cracked-machine/DigitalCurrentSinkV3/HW/docs/3D/CurrentSinkModule2.png

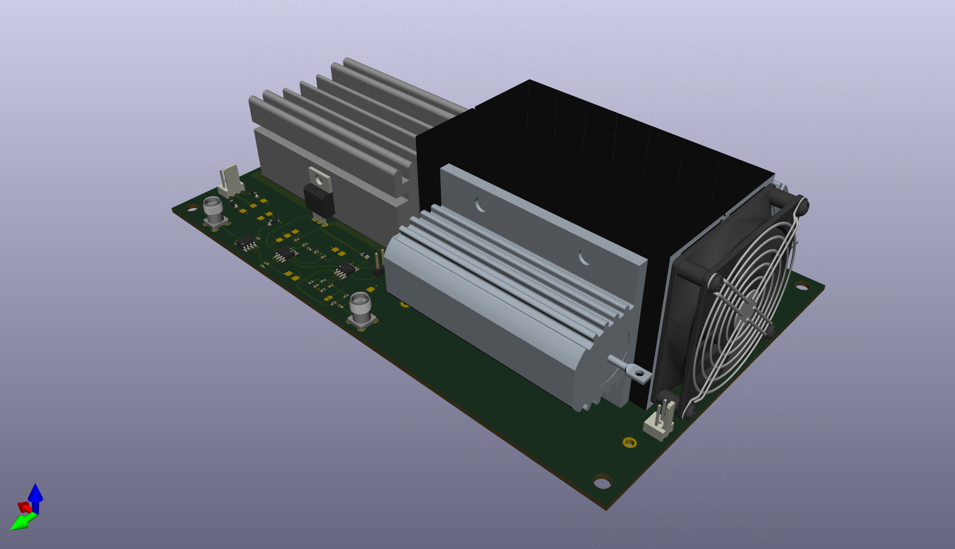
HW/docs/3D/CurrentSinkModule2.png
