cracked-machine/DigitalCurrentSinkV3/CAD/ControlModuleFrontPanel/doc/3D/ControlModuleFrontPanel_Notations.png

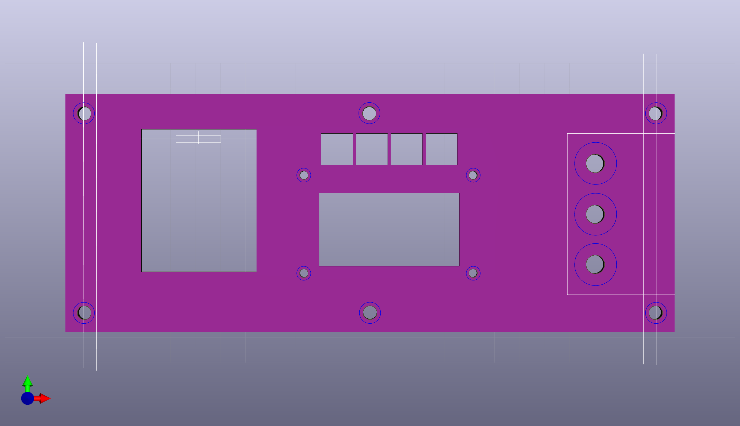
CAD/ControlModuleFrontPanel/doc/3D/ControlModuleFrontPanel_Notations.png
