cracked-machine/DigitalCurrentSinkV3/CAD/ControlModuleFrontPanel/doc/3D/ControlModuleFrontPanel_Realistic.png

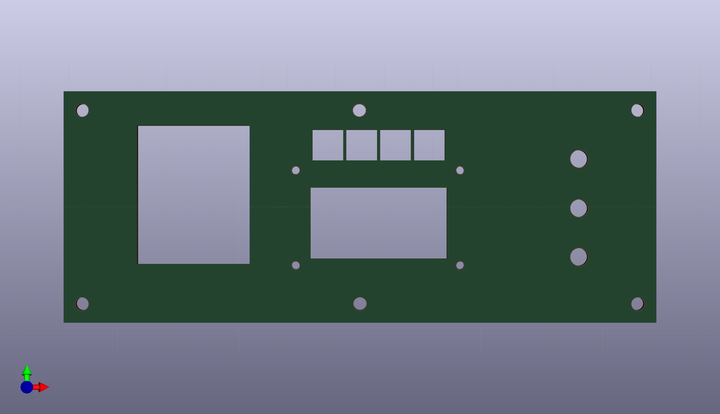
CAD/ControlModuleFrontPanel/doc/3D/ControlModuleFrontPanel_Realistic.png
