cracked-machine/DigitalCurrentSinkV3/HW/docs/3D/CurrentSinkModule.png

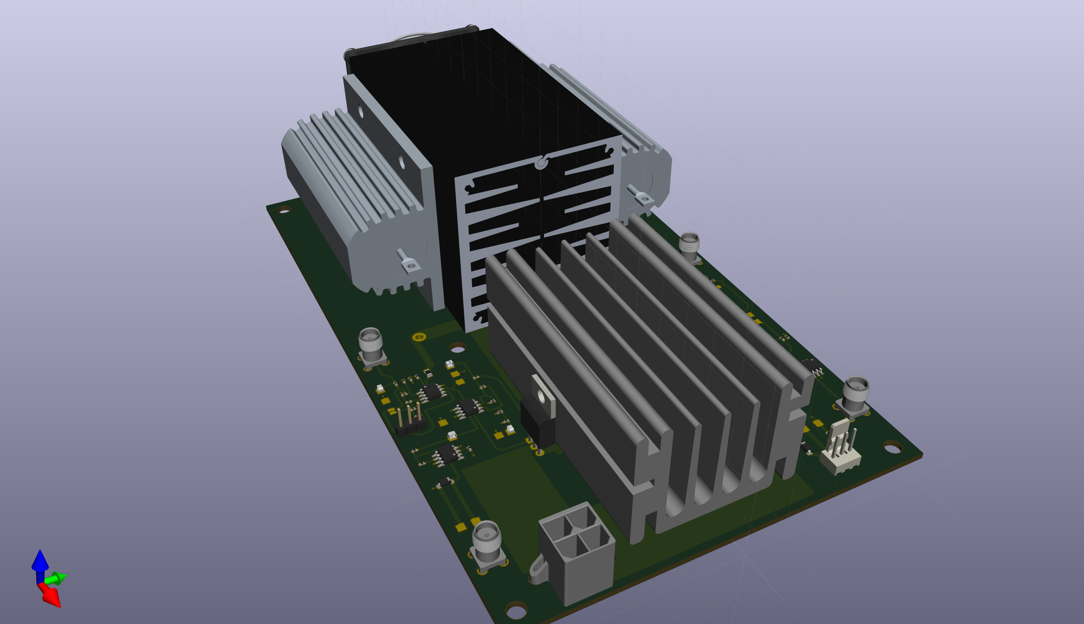
HW/docs/3D/CurrentSinkModule.png
