cracked-machine/DigitalCurrentSinkV3/HW/Simulation/ADA4522/NonInvertingx10Gain/NonInvertingx1.5Gain_GainAndNoise.png

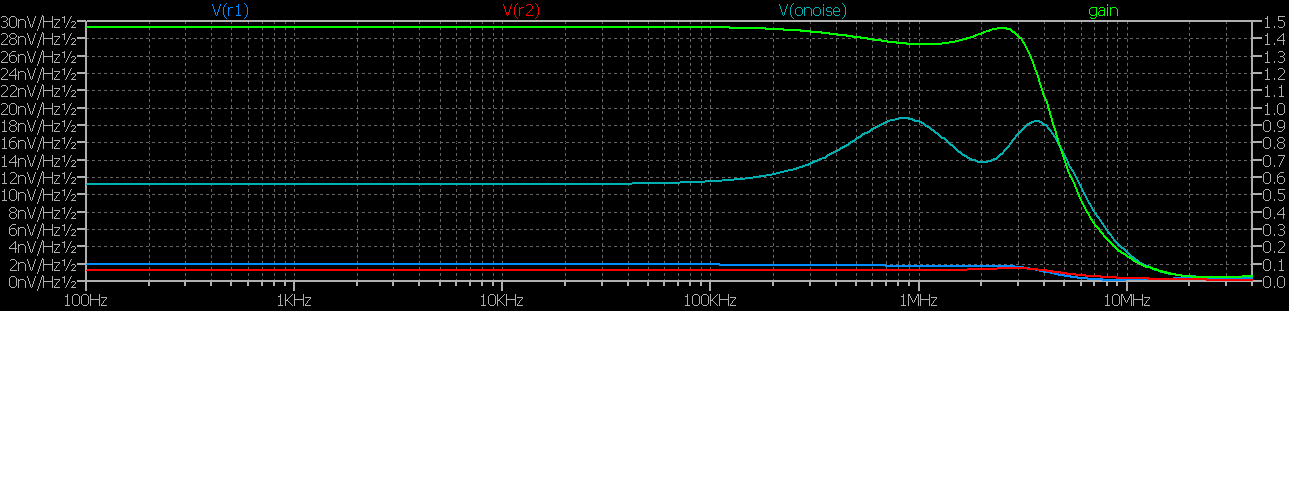
HW/Simulation/ADA4522/NonInvertingx10Gain/NonInvertingx1.5Gain_GainAndNoise.png
