cracked-machine/DigitalCurrentSinkV3/HW/Simulation/ADA4522/NonInvertingx10Gain/NonInvertingx10Gain.png

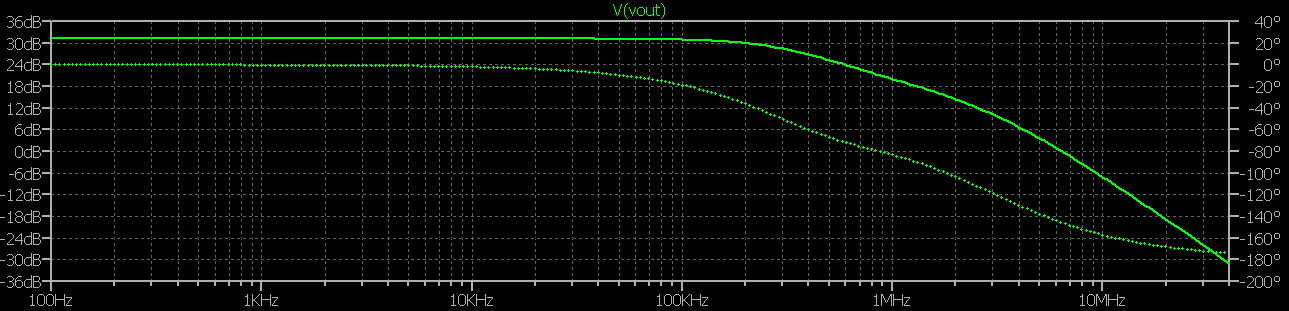
HW/Simulation/ADA4522/NonInvertingx10Gain/NonInvertingx10Gain.png
