cracked-machine/DigitalCurrentSinkV3/HW/Simulation/CurrentSenseResistor/LowSide.png

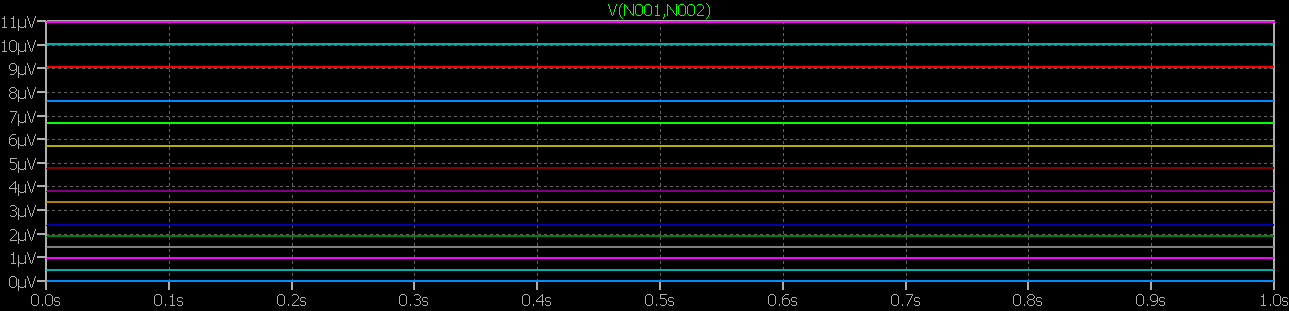
HW/Simulation/CurrentSenseResistor/LowSide.png
