cracked-machine/DigitalCurrentSinkV3/HW/Simulation/LTC2058/NonInvertingUnityGain/NonInvertingUnityGain_FreqVsGainAndNoise_Output.png

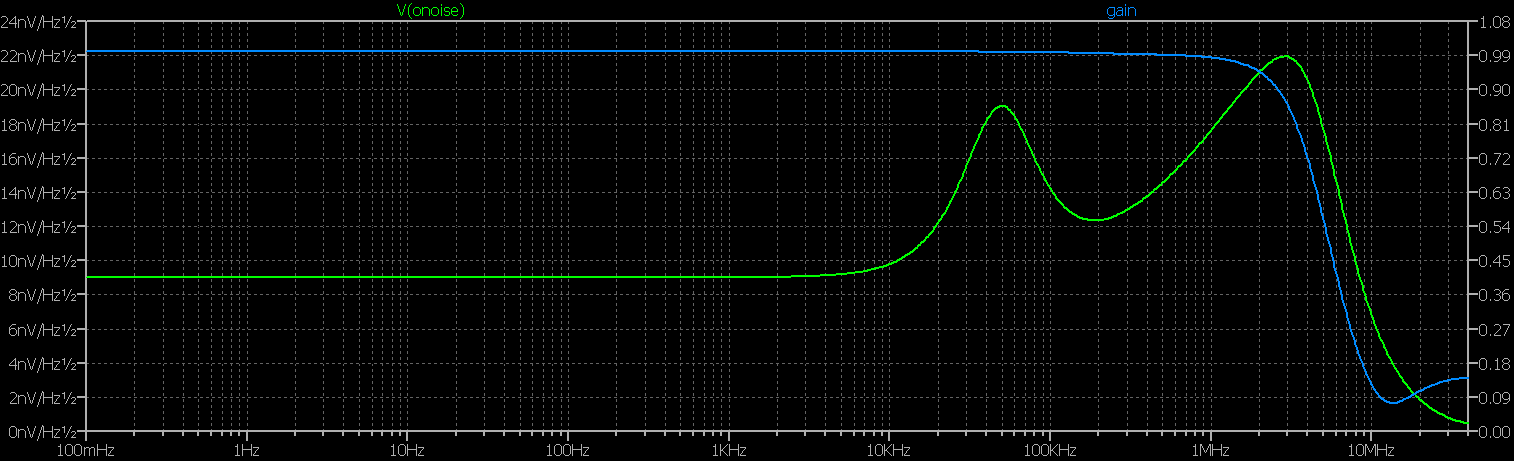
HW/Simulation/LTC2058/NonInvertingUnityGain/NonInvertingUnityGain_FreqVsGainAndNoise_Output.png
