cracked-machine/DigitalCurrentSinkV3/HW/Simulation/ADA4522/FirstOrderSK_LowPass/1stOrderLowsPass_NoiseRange1K_50K.png

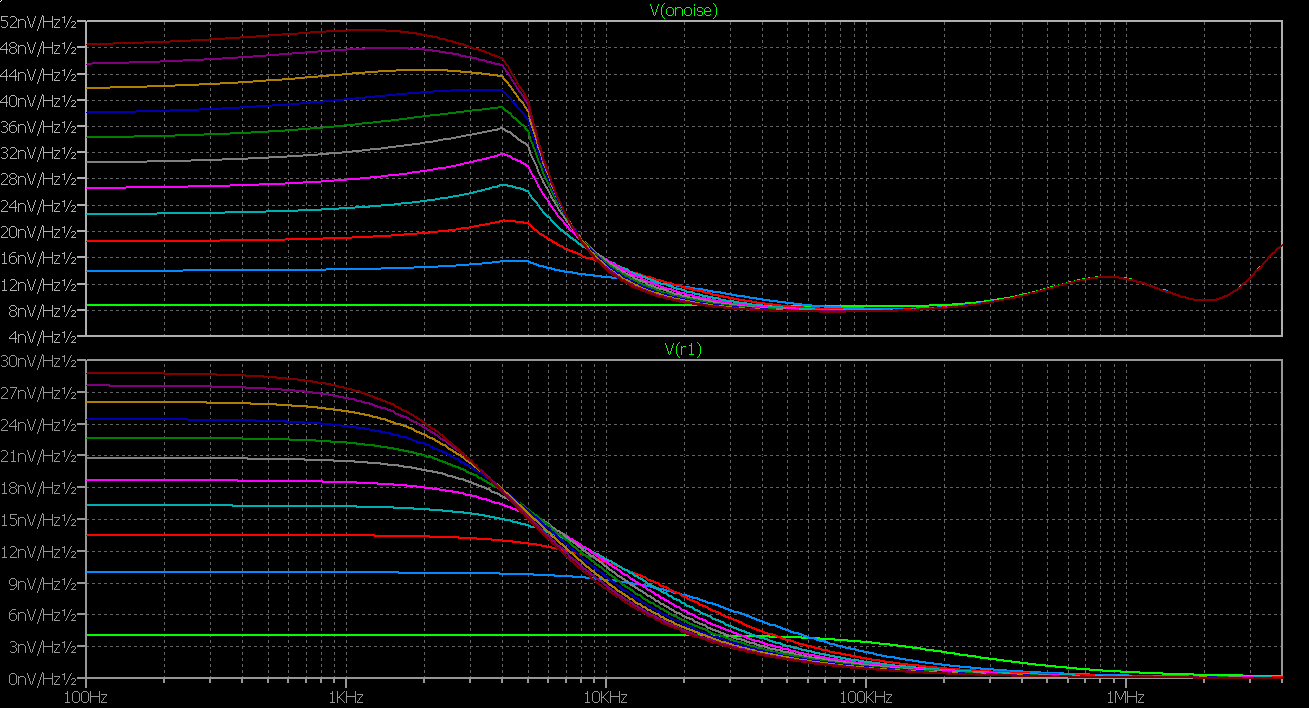
HW/Simulation/ADA4522/FirstOrderSK_LowPass/1stOrderLowsPass_NoiseRange1K_50K.png
