cracked-machine/DigitalCurrentSinkV3/HW/Simulation/ADA4522/FirstOrderSK_LowPass/1stOrderLowsPass_NoiseRange10R_100R.png

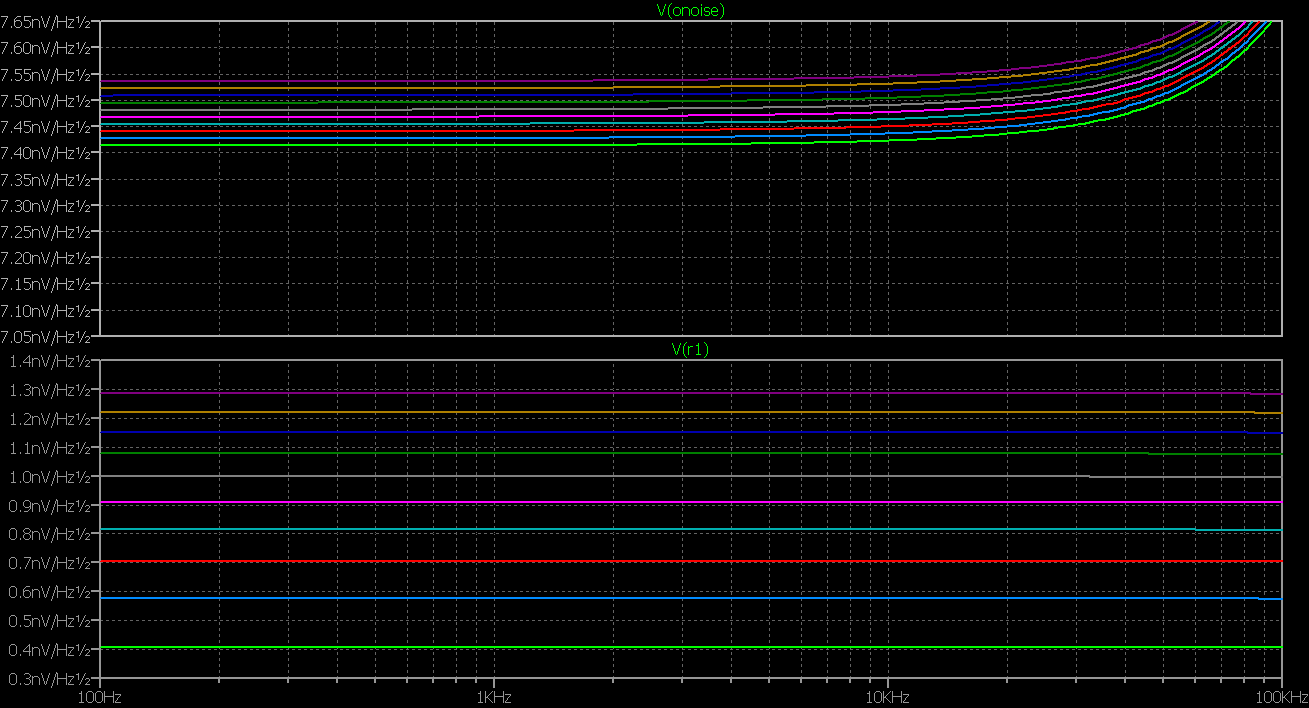
HW/Simulation/ADA4522/FirstOrderSK_LowPass/1stOrderLowsPass_NoiseRange10R_100R.png
