cracked-machine/DigitalCurrentSinkV3/HW/Simulation/ADA4522/SecondOrderSK_LowPass/2ndOrderSKLowPass_NoiseAndAtten_100R_10u.png

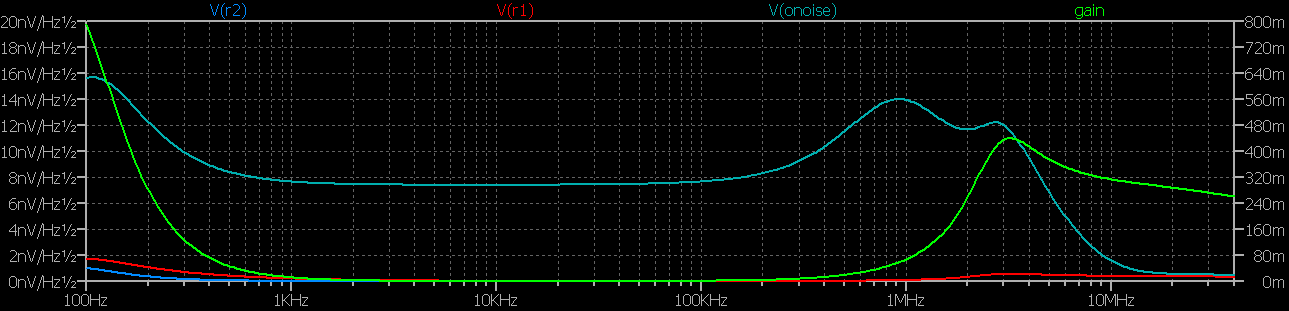
HW/Simulation/ADA4522/SecondOrderSK_LowPass/2ndOrderSKLowPass_NoiseAndAtten_100R_10u.png
