cracked-machine/DigitalCurrentSinkV3/HW/Simulation/LT1007/2ndOrderSKLowPass_/2ndOrderSKLowPass_NoiseAndAtten_1K_100n.png

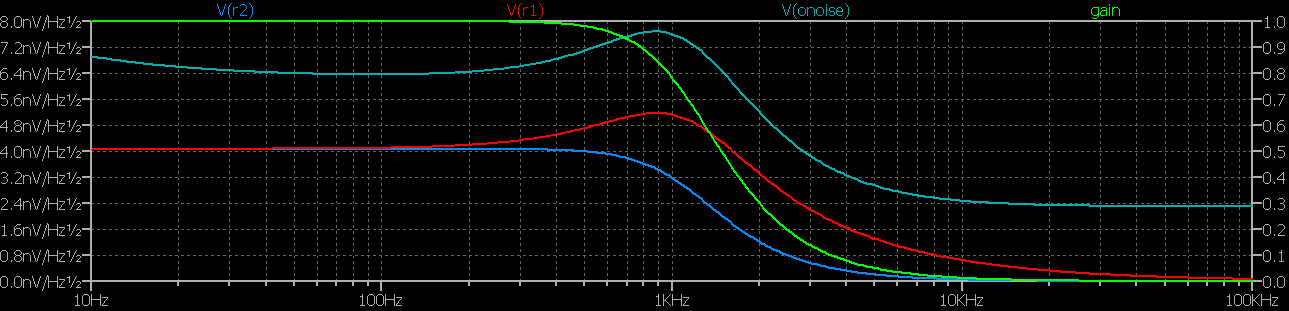
HW/Simulation/LT1007/2ndOrderSKLowPass_/2ndOrderSKLowPass_NoiseAndAtten_1K_100n.png
