cracked-machine/DigitalCurrentSinkV3/HW/Simulation/LTC2058/SecondOrderSK_LowPass/2ndOrderLowsPass_Noise100RWith0_10u.png

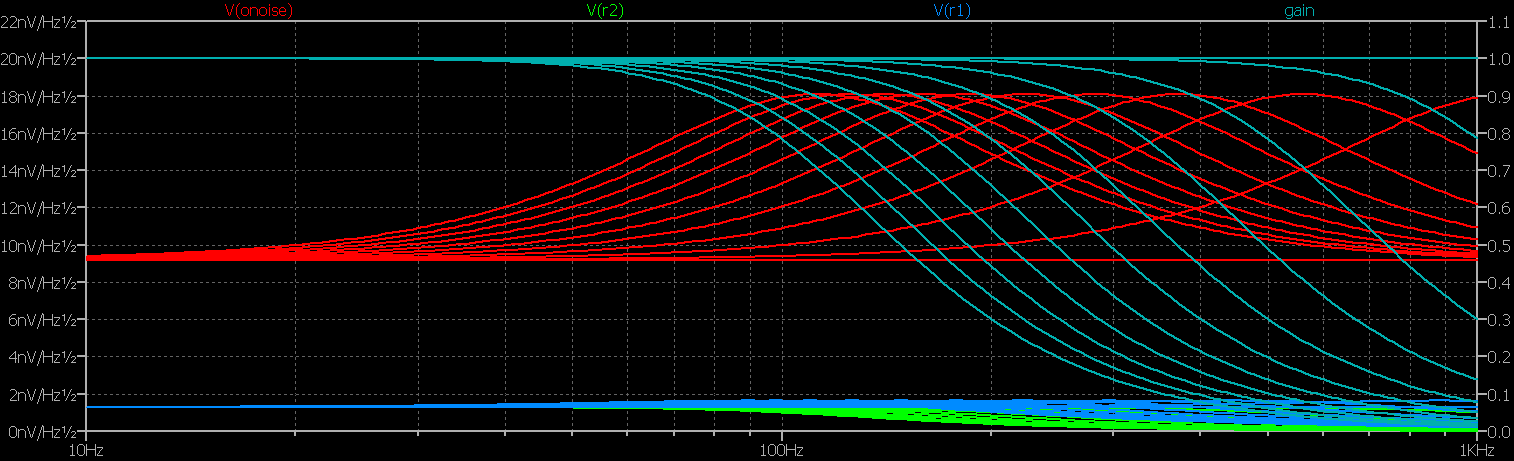
HW/Simulation/LTC2058/SecondOrderSK_LowPass/2ndOrderLowsPass_Noise100RWith0_10u.png
