cracked-machine/DigitalCurrentSinkV3/HW/Simulation/LTC2058/SecondOrderSK_LowPass/2ndOrderLowsPass_UnityGainAndNoise2x100RWith10u_AndResistorNoiseContributions.png

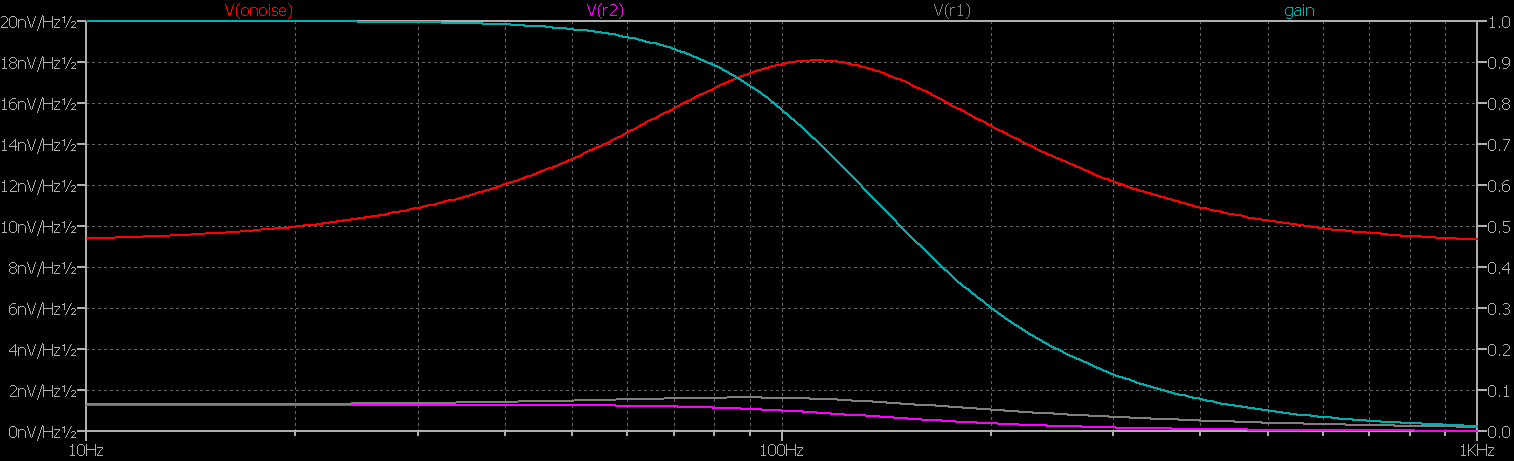
HW/Simulation/LTC2058/SecondOrderSK_LowPass/2ndOrderLowsPass_UnityGainAndNoise2x100RWith10u_AndResistorNoiseContributions.png
