cracked-machine/DigitalCurrentSinkV3/HW/Simulation/ADA4522/FirstOrderSK_LowPass/FirstOrderSK_LowPass.asc

C2: cap; {C1}
R1: res; 100R
U1: ADA4522-1
V1: voltage; 2.5
V2: voltage; 2.5
V3: voltage; ""; AC 1
Named nets: 0, V-, V+, Vout, Vin
.ac dec 100 100 40e6
.noise V(Vout) V3 dec 100 10 10K
.step param C1 0u 10u 1u
