cracked-machine/DigitalCurrentSinkV3/HW/Simulation/ADA4522/SecondOrderSK_LowPass/DRAFT13.ASC

C1: cap; 2n
C2: cap; 1n
R1: res; 5K
R2: res; 5K
U1: LT6020
V1: voltage; 5
V2: voltage; 5
V4: signal; SINE(0 1 100)
Named nets: 0, Vout, Vin, V+, V-
.tran 2
