cracked-machine/DigitalCurrentSinkV3/HW/Simulation/ADA4522/SecondOrderSK_LowPass/SecondOrderSK_LowPass.asc

C1: cap; 2µ
C2: cap; 1µ
R1: res; 10k
R2: res; 10k
U1: ADA4522-1
V1: voltage; 12
V2: voltage; 12
V3: voltage; ""; AC 1
Named nets: 0, V-, V+, Vout, Vin
.ac dec 100 100 40e6
.noise V(Vout) V3 dec 100 10 1K
