cracked-machine/DigitalCurrentSinkV3/HW/Simulation/LT1007/2ndOrderSKLowPass_/SecondOrderSK_LowPass.asc

C1: cap; 200n
C2: cap; 100n
R1: res; 1K
R2: res; 1K
U2: LT1007
V1: voltage; 12
V2: voltage; 12
V3: voltage; ""; AC 1
Named nets: 0, V-, V+, Vout, Vin
.ac dec 100 100 40e6
.noise V(Vout) V3 dec 100 10 100K
