cracked-machine/DigitalCurrentSinkV3/HW/Simulation/LTC2058/2ndOrderSK_LowPassWithSeperateGainStage/2ndOrderSK_LPFWithSeperateGainStage.asc

C1: cap; 20µ
C2: cap; 10µ
R1: res; 100R
R2: res; 100R
R3: res; 220R
R4: res; 470R
U1: LTC2058
U3: LTC2058
V1: voltage; 12
V2: voltage; 12
V3: voltage; ""; AC 1
Named nets: 0, V-, V+, Vout2, Vin, Vout1
.ac dec 100 100 40e6
;noise V(Vout1) V3 dec 100 10 1K
.STEP PARAM C1 0u 10u 1u
.noise V(Vout1) V3 dec 100 10 1K
