cracked-machine/DigitalCurrentSinkV3/HW/Simulation/ADA4522/SecondOrderSK_LowPass/DRAFT14.ASC

Q1: npn
V1: voltage; {Vin}
V2: voltage; 12V
Named nets: 0, V+
