cracked-machine/DigitalCurrentSinkV3/HW/Simulation/LTC2058/SecondOrderSK_LowPass/SecondOrderSK_LowPass.asc

C1: cap; {C1*2}
C2: cap; {C1}
R1: res; 100R
R2: res; 100R
R4: res; 220R
R5: res; 470R
U1: LTC2058
V1: voltage; 12
V2: voltage; 12
V3: voltage; ""; AC 1
Named nets: 0, V-, V+, Vout, Vin
.ac dec 100 100 40e6
.noise V(Vout) V3 dec 100 10 1K
.STEP PARAM C1 0u 10u 1u
