cracked-machine/DigitalCurrentSinkV3/HW/Simulation/MOSFET_CurrentSense_NoSignalInversion_AD8421.asc

M1: nmos
M2: pmos
R1: res; 0.33R
R2: res; 0.33R
R3: res; 10R
R4: res; 10R
U1: LTC2058
U2: LTC2058
U3: AD8421
U4: AD8421
V1: voltage; 15V
V2: voltage; 5V
V3: voltage; 5V
V4: voltage; {VPOSIN}
V5: voltage; 15V
V6: voltage; {VPOSIN}
Named nets: 0, V-, V+, VPOSOUT, VNEGOUT
.tran 1
.STEP PARAM VPOSIN 0.5 5 0.5
