cracked-machine/DigitalCurrentSinkV3/HW/Simulation/CurrentSenseResistor/CurrentSenseResistor_HighSide.ASC

C1: cap; 10n
C2: cap; 1n
C3: cap; 1n
C4: cap; 10n
C5: cap; 1n
C6: cap; 1n
M1: nmos
M2: pmos
R1: res; {Rsense}
R2: res; 5R
R3: res; 33R
R4: res; 33R
R5: res; {Rsense}
R6: res; 5R
R7: res; 33R
R8: res; 33R
R9: res; 50R
R10: res; 50R
R11: res; 10K
R12: res; 1K
U1: AD8421
U2: AD8421
U3: LTC2058
U4: LTC2058
V1: voltage; {VIn}
V2: voltage; {SUTVS}
V3: voltage; 12
V4: voltage; 12
V5: voltage; 0.1
V6: voltage; {VIn}
V7: voltage; {SUTVS}
Named nets: 0, V-, V+, VPosOut, VNegOut
.STEP PARAM VIn 0 5 0.5
.TRAN 1
.PARAM SUTVS 9
.PARAM Rsense 0.1R
