cracked-machine/DigitalCurrentSinkV3/HW/Simulation/CurrentSenseResistor/DRAFT1.ASC

D1: LED
R1: res; 10R
V1: voltage; 4
Named nets: 0
.tran 1
