cracked-machine/DigitalCurrentSinkV3/HW/Simulation/CurrentSenseResistor/DRAFT2.ASC

C1: cap; 1µ
C2: cap; 10µ
C3: cap; 100n
Q1: npn; 2N2222
R1: res; 20K
R2: res; 1Meg
R3: res; 20K
R4: res; 3K
R5: res; 1K
V1: voltage; SINE(0 100m 440)
V2: voltage; 9
Named nets: 0, Vin, Vout
.tran 250ms
