cracked-machine/DigitalCurrentSinkV3/HW/Simulation/AD8421/UnityGain/UnityGain.asc

R1: res; 0.1R
U2: AD8421
V1: voltage; 12
V2: voltage; 12
Vin_source: voltage; {Vin_source}
Named nets: 0, V-, V+, Vout, Vin
.ac dec 100 100k 40e6
.noise V(Vout) Vin_source dec 100 0.1 40Meg
.tran .2
.step param Vin_source 0.1 3.3 0.1
