cracked-machine/DigitalCurrentSinkV3/HW/Simulation/AD8421/UnityGainWithInputFilter/UnityGainWithInputFilter.asc

C1: cap; 10n
C2: cap; 1n
C3: cap; 1n
R1: res; 0.1R
R2: res; 33R
R3: res; 33R
U2: AD8421
V1: voltage; 12
V2: voltage; 12
Vin_source: voltage; {Vin_source}
Named nets: 0, V-, V+, Vout, Vin
.ac dec 100 100k 40e6
.noise V(Vout) Vin_source dec 100 0.1 40Meg
.tran .2
.step param Vin_source 0.1 3.3 0.1
