cracked-machine/DigitalCurrentSinkV3/HW/Simulation/LTC2058/CurrentSenseResistor/CurrentSenseResistor_HighSide.ASC

M1: nmos
R1: res; 0.1
V1: voltage; {Vin}
V2: voltage; 5
Named nets: 0
.STEP PARAM Vin 0.2 3.3 0.2
.TRAN 1
