cracked-machine/DigitalCurrentSinkV3/HW/Simulation/LTC2058/DifferentialUnityGain/DifferentialUnityGain.asc

C1: cap; 10n
C2: cap; 100n
R1: res; 0.1R
R2: res; {Rx}
R3: res; {Rx}
R4: res; {Rx}
R5: res; {Rx}
R6: res; 22
U1: LTC2058
V1: voltage; 12
V2: voltage; 12
Vin_source: voltage; {Vsin}
Named nets: 0, V-, V+, Vout, Vin
.ac dec 100 100k 40e6
.noise V(Vout) Vin_source dec 100 0.1 40Meg
.tran 0.5
.STEP PARAM Vsin -0.1 -3.3 0.1
.param Rx=82R
