cracked-machine/DigitalCurrentSinkV3/HW/Simulation/LTC2058/DifferentialUnityGain/DRAFT2.ASC

D1: diode; 1N4148
R1: res; 10R
R2: res; 0.1R
R3: res; 10R
R4: res; 1K
U1: LTC2058
V1: voltage; 12
V2: voltage; 12
Vin: voltage; {Vsource}
Named nets: 0, V+, Vout, V-
.tran 1
.STEP PARAM Vsource 0..2 3.2 0.2
