cracked-machine/DigitalCurrentSinkV3/SW/STM32L496_DigitalCurrentSinkV3/Inc/SystemConstants.h

/*
 * SystemConstants.h
 *
 *  Created on: Aug 25, 2019
 *      Author: chris
 */

#ifndef SYSTEMCONSTANTS_H_
#define SYSTEMCONSTANTS_H_

/* Max resolution for 16-bit timer */
#define TIMRES 				65535

/* MCU clock speed in hertz */
#define MASTERCLK 			80000000

/* DAC VREF */
#define VREF 				3.3

/* DAC resolution */
#define DACRES 				4096

/* ADC Resolution */
#define ADCRES				4095

/* increment amounts for nudging voltage/frequency values */
#define MAXFREQSTEP 		32
#define MAXAMPSTEP 			1

// adjust to match power resistor value, allows for variation according to tolerances
#define CH0_PWR_RESISTOR	0.12 	// positive N-channel
#define CH0_RESISTOR_ERR	0.0	// tolerance compensation
#define CH1_PWR_RESISTOR	0.1 	// negative P-channel
#define CH1_RESISTOR_ERR	0.00	// tolerance compensation

/* instrumentation amp gain compensation.
 * This can be done in HW using gain resistor or "fixed" here in SW
 * Absolute minimum value is 1 */
#define CH0_INAMP_GAIN_COMP		8.8
#define CH1_INAMP_GAIN_COMP		6.8

/* prescaler for RAND and AUTO modes. RAND PSC should be much larger than AUTO PSC */
#define TIM_PSC_RANDMODE	16383
#define TIM_PSC_AUTOMODE	1023

// not used
#define MAX_WATTAGE			36

// not used
void SYS_Init();

#endif /* SYSTEMCONSTANTS_H_ */
