cracked-machine/DigitalCurrentSinkV3/SW/STM32L496_DigitalCurrentSinkV3/Src/utils.c

/*
 * utils.c
 *
 *  Created on: 20 Mar 2019
 *      Author: Chris Sutton
 */


#include "utils.h"
#include "tim.h"
#include "stm32l4xx_hal.h"
#include "dac.h"
#include "ssd1306_tests.h"
#include "ssd1306.h"
#include "adc.h"

void HAL_GPIO_WRITE_ODR(GPIO_TypeDef* GPIOx, uint16_t GPIO_Pin);

//uint32_t adc_out[2] = {};



////////////////////////////////////////////////////////
///
///	Name: _write
///
/// Description: Redirect stdout to ITM/SWO
///
////////////////////////////////////////////////////////

void Utils_Init()
{




	//HAL_GPIO_TogglePin(GPIOB, GPIO_PIN_7);
	// start DAC and associated timers
	HAL_TIM_Base_Start_IT(&htim6);
	HAL_TIM_Base_Start_IT(&htim7);



	DAC_ChannelConfTypeDef sConfig = {0};
	HAL_DACEx_SelfCalibrate(&hdac1, &sConfig, DAC_CHANNEL_1);
	HAL_DACEx_SelfCalibrate(&hdac1, &sConfig, DAC_CHANNEL_2);
	HAL_DAC_Start(&hdac1,DAC_CHANNEL_1);
	HAL_DAC_Start(&hdac1,DAC_CHANNEL_2);

	DU_SetVoltagePreview(DAC_CHANNEL_1, 0.0f);
	DU_SetVoltage(DAC_CHANNEL_1);
	DU_SetVoltagePreview(DAC_CHANNEL_2, 0.0f);
	DU_SetVoltage(DAC_CHANNEL_2);


	HAL_Delay(3000);	// I2C needs to delay before initializing the display
	//printf("Initialising Display...\n");

	HAL_GPIO_WritePin(OLED_RST_GPIO_Port, OLED_RST_Pin, GPIO_PIN_RESET);
	HAL_Delay(10);
	HAL_GPIO_WritePin(OLED_RST_GPIO_Port, OLED_RST_Pin, GPIO_PIN_SET);
	HAL_Delay(10);

	Utils_i2c_scan();
	ssd1306_Init();


	// OLED display timer
	HAL_TIM_Base_Start_IT(&htim5);

	// display blink counter
	HAL_TIM_Base_Start_IT(&htim16);

	// debounce counter
	HAL_TIM_Base_Start_IT(&htim17);

	HAL_ADCEx_Calibration_Start(&hadc1, ADC_SINGLE_ENDED);
	HAL_ADC_Start_DMA(&hadc1, AU_GetADCOut(), 2);


}




////////////////////////////////////////////////
///
///		Utils_i2c_scan
///
////////////////////////////////////////////////


void Utils_i2c_scan() {
    printf("Scanning I2C bus...\n");
    char msg[64];
    int DeviceFound=0;
    char notFound[160];
    HAL_StatusTypeDef res;
    for(uint16_t i = 0; i < 128; i++) {
        res = HAL_I2C_IsDeviceReady(&hi2c1, i << 1, 1, 10);
        if(res == HAL_OK) {

            snprintf(msg, sizeof(msg), "0x%02X", i);
            printf("Found %s\n", msg);
            DeviceFound=1;
            ssd1306_SetI2CAddress(i);

        }
        if(res == HAL_ERROR)
        {
        	//printf("%d: No device found\n", i);

        }
    }
    if(!DeviceFound)
    {

    	printf("%s\n", notFound);
    	printf("No device found\n");
    }
}

////////////////////////////////////////////////////////
///
///	Name: _write
///
/// Description: Redirect stdout to ITM/SWO
///
////////////////////////////////////////////////////////

int _write(int file, char *ptr, int len)
{
	for (int i=0; i<len; i++)
	{
		ITM_SendChar((*ptr++));
	}
	return len;
}


/* USER CODE BEGIN 1 */
/**
1. Disable the I2C peripheral by clearing the PE bit in I2Cx_CR1 register.
2. Configure the SCL and SDA I/Os as General Purpose Output Open-Drain, High level
(Write 1 to GPIOx_ODR).
3. Check SCL and SDA High level in GPIOx_IDR.
4. Configure the SDA I/O as General Purpose Output Open-Drain, Low level (Write 0 to
GPIOx_ODR).
5. Check SDA Low level in GPIOx_IDR.
6. Configure the SCL I/O as General Purpose Output Open-Drain, Low level (Write 0 to
GPIOx_ODR).
7. Check SCL Low level in GPIOx_IDR.
8. Configure the SCL I/O as General Purpose Output Open-Drain, High level (Write 1 to
GPIOx_ODR).
9. Check SCL High level in GPIOx_IDR.
10. Configure the SDA I/O as General Purpose Output Open-Drain , High level (Write 1 to
GPIOx_ODR).
11. Check SDA High level in GPIOx_IDR.
12. Configure the SCL and SDA I/Os as Alternate function Open-Drain.
13. Set SWRST bit in I2Cx_CR1 register.
14. Clear SWRST bit in I2Cx_CR1 register.
15. Enable the I2C peripheral by setting the PE bit in I2Cx_CR1 register.
**/
void HAL_I2C_ClearBusyFlagErrata_2_14_7(I2C_HandleTypeDef *hi2c) {

    static uint8_t resetTried = 0;
    if (resetTried == 1) {
        return ;
    }
    uint32_t SDA_PIN = GPIO_PIN_7;
    uint32_t SCL_PIN = GPIO_PIN_6;
    GPIO_InitTypeDef GPIO_InitStruct;

    // 1
    __HAL_I2C_DISABLE(hi2c);

    // 2
    GPIO_InitStruct.Pin = SDA_PIN|SCL_PIN;
    GPIO_InitStruct.Mode = GPIO_MODE_OUTPUT_OD;
    GPIO_InitStruct.Pull = GPIO_NOPULL;
    GPIO_InitStruct.Speed = GPIO_SPEED_FAST;
    HAL_GPIO_Init(GPIOB, &GPIO_InitStruct);

    HAL_GPIO_WRITE_ODR(GPIOB, SDA_PIN);
    HAL_GPIO_WRITE_ODR(GPIOB, SCL_PIN);

    // 3
    //GPIO_PinState pinState;
    if (HAL_GPIO_ReadPin(GPIOB, SDA_PIN) == GPIO_PIN_RESET) {
        for(;;){}
    }
    if (HAL_GPIO_ReadPin(GPIOB, SCL_PIN) == GPIO_PIN_RESET) {
        for(;;){}
    }

    // 4
    GPIO_InitStruct.Pin = SDA_PIN;
    HAL_GPIO_Init(GPIOB, &GPIO_InitStruct);

    HAL_GPIO_TogglePin(GPIOB, SDA_PIN);

    // 5
    if (HAL_GPIO_ReadPin(GPIOB, SDA_PIN) == GPIO_PIN_SET) {
        for(;;){}
    }

    // 6
    GPIO_InitStruct.Pin = SCL_PIN;
    HAL_GPIO_Init(GPIOB, &GPIO_InitStruct);

    HAL_GPIO_TogglePin(GPIOB, SCL_PIN);

    // 7
    if (HAL_GPIO_ReadPin(GPIOB, SCL_PIN) == GPIO_PIN_SET) {
        for(;;){}
    }

    // 8
    GPIO_InitStruct.Pin = SDA_PIN;
    HAL_GPIO_Init(GPIOB, &GPIO_InitStruct);

    HAL_GPIO_WRITE_ODR(GPIOB, SDA_PIN);

    // 9
    if (HAL_GPIO_ReadPin(GPIOB, SDA_PIN) == GPIO_PIN_RESET) {
        for(;;){}
    }

    // 10
    GPIO_InitStruct.Pin = SCL_PIN;
    HAL_GPIO_Init(GPIOB, &GPIO_InitStruct);

    HAL_GPIO_WRITE_ODR(GPIOB, SCL_PIN);

    // 11
    if (HAL_GPIO_ReadPin(GPIOB, SCL_PIN) == GPIO_PIN_RESET) {
        for(;;){}
    }

    // 12
    GPIO_InitStruct.Pin = SDA_PIN|SCL_PIN;
    GPIO_InitStruct.Mode = GPIO_MODE_AF_OD;
    GPIO_InitStruct.Alternate = GPIO_AF4_I2C1;
    HAL_GPIO_Init(GPIOB, &GPIO_InitStruct);

   // 13
   hi2c->Instance->CR1 |= I2C_CR1_SWRST;

   // 14
   hi2c->Instance->CR1 ^= I2C_CR1_SWRST;

   // 15
   __HAL_I2C_ENABLE(hi2c);

   resetTried = 1;
}

void HAL_GPIO_WRITE_ODR(GPIO_TypeDef* GPIOx, uint16_t GPIO_Pin)
{
  /* Check the parameters */
  assert_param(IS_GPIO_PIN(GPIO_Pin));

  GPIOx->ODR |= GPIO_Pin;
}
