cracked-machine/DigitalCurrentSinkV3/SW/STM32L496_DigitalCurrentSinkV3/Inc/utils.h

/*
 * utils.h
 *
 *  Created on: 20 Mar 2019
 *      Author: chris
 */





#ifndef UTILS_H_
#define UTILS_H_

#include "stm32l4xx_hal.h"
#include "ssd1306.h"
#include <string.h>
#include <stdarg.h>
#include <DacUtilities.h>
#include "ADCUtilities.h"
//uint32_t adc_out[2];




void Utils_Init();
int _write(int file, char *ptr, int len);
void Utils_i2c_scan();
void HAL_I2C_ClearBusyFlagErrata_2_14_7(I2C_HandleTypeDef *hi2c);

#endif /* UTILS_H_ */
